hstarmans/rotorbalancer/MMA8452Q.py

# Author: Rik Starmans
# Date: 3-1-2020
# Original code https://github.com/ControlEverythingCommunity/MMA8452Q/blob/master/Python/MMA8452Q.py
import smbus
import time


class Accelsensor:
    def __init__(self):
        # Get I2C bus
        self.bus = smbus.SMBus(1)
        self.address = 0x1d
        # MMA8452Q address
        # Select Control register, 0x2A(42)
        #		0x00(00)	StandBy mode
        self.bus.write_byte_data(self.address, 0x2A, 0x00)
        # MMA8452Q address, 0x1C(28)
        # Select Control register, 0x2A(42)
        #		0x01(01)	Active mode
        self.bus.write_byte_data(self.address, 0x2A, 0x01)
        # MMA8452Q address, 0x1C(28)
        # Select Configuration register, 0x0E(14)
        #		0x00(00)	Set range to +/- 2g
        self.bus.write_byte_data(self.address, 0x0E, 0x00)
        time.sleep(0.5)

    def get_acceleration(self):
        # MMA8452Q address)
        # Read data back from 0x00(0), 7 bytes
        # Status register, X-Axis MSB, X-Axis LSB, Y-Axis MSB, Y-Axis LSB, Z-Axis MSB, Z-Axis LSB
        data = self.bus.read_i2c_block_data(self.address, 0x00, 7)
        # Convert the data
        xAccl = (data[1] * 256 + data[2]) / 16
        if xAccl > 2047 :
            xAccl -= 4096
        yAccl = (data[3] * 256 + data[4]) / 16
        if yAccl > 2047 :
            yAccl -= 4096
        zAccl = (data[5] * 256 + data[6]) / 16
        if zAccl > 2047 :
            zAccl -= 4096
        return [xAccl, yAccl, zAccl]
